haldarsaurav/Headway/docs/images/screen_boot.png

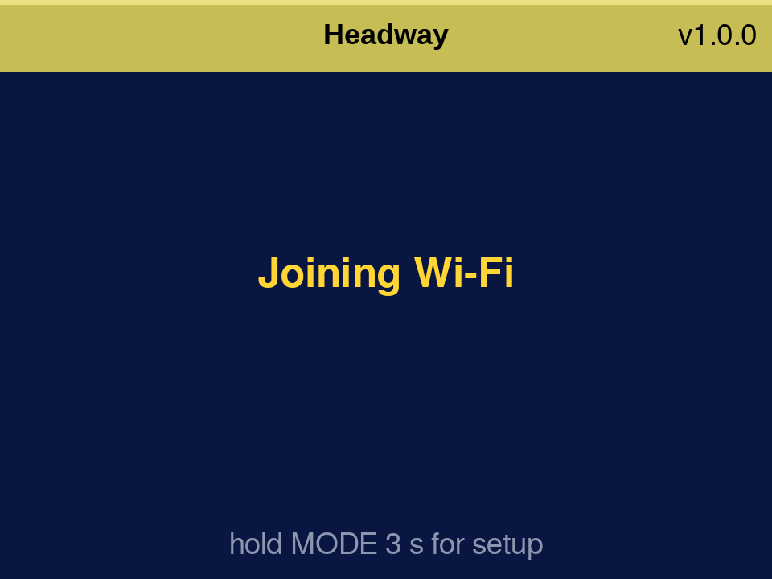
docs/images/screen_boot.png
