haldarsaurav/Headway/docs/previews_v1.2.6/A_2b_trains_p2.png

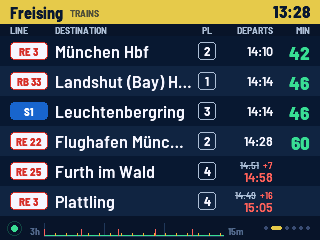
docs/previews_v1.2.6/A_2b_trains_p2.png
