haldarsaurav/Headway/docs/previews_v1.2.6/A_5_weather_stress.png

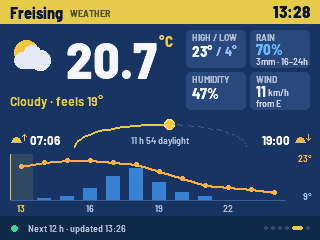
docs/previews_v1.2.6/A_5_weather_stress.png
