haldarsaurav/Headway/docs/previews_v1.2.6/A_6_outlook_stress.png

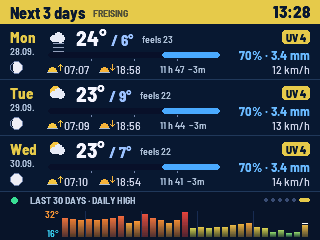
docs/previews_v1.2.6/A_6_outlook_stress.png
