haldarsaurav/Headway/docs/previews_v1.2.6/A_7_hold.png

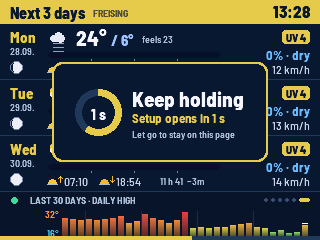
docs/previews_v1.2.6/A_7_hold.png
