haldarsaurav/Headway/docs/previews_v1.2.6/A_9_empty.png

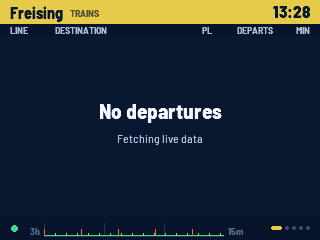
docs/previews_v1.2.6/A_9_empty.png
