haldarsaurav/Headway/docs/previews_v1.2.6/B_3_stadtbus_scroll.png

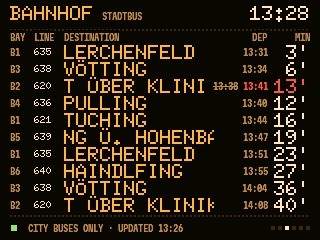
docs/previews_v1.2.6/B_3_stadtbus_scroll.png
