haldarsaurav/Headway/docs/previews_v1.2.6/B_4_pr_scroll.png

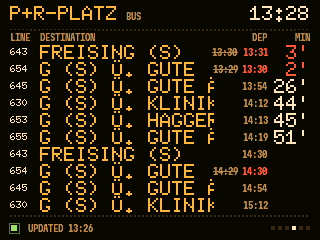
docs/previews_v1.2.6/B_4_pr_scroll.png
