haldarsaurav/Headway/docs/previews_v1.2.6/B_6_outlook_stress.png

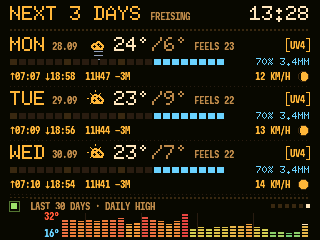
docs/previews_v1.2.6/B_6_outlook_stress.png
