haldarsaurav/Headway/docs/previews_v1.2.6/B_9_empty.png

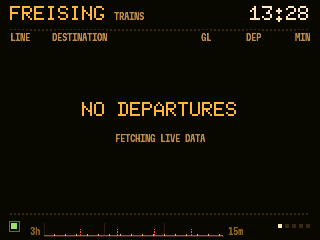
docs/previews_v1.2.6/B_9_empty.png
