haldarsaurav/Headway/docs/previews_v1.2.6/C_4_pr_scroll_stress.png

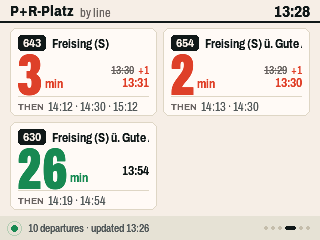
docs/previews_v1.2.6/C_4_pr_scroll_stress.png
