haldarsaurav/Headway/docs/previews_v1.2.6/C_7_hold.png

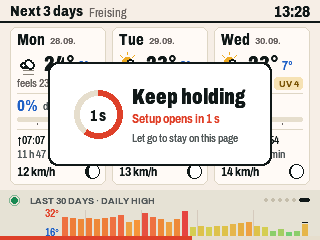
docs/previews_v1.2.6/C_7_hold.png
