haldarsaurav/Headway/docs/previews_v1.2.6/F_2_trains_flip.png

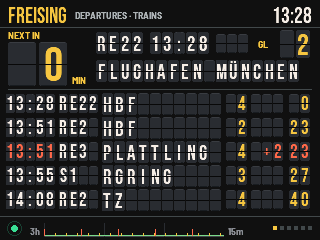
docs/previews_v1.2.6/F_2_trains_flip.png
