haldarsaurav/Headway/docs/previews_v1.2.6/F_3_stadtbus_flip.png

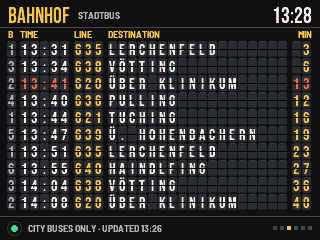
docs/previews_v1.2.6/F_3_stadtbus_flip.png
