haldarsaurav/Headway/docs/previews_v1.2.6/F_4_pr_flip.png

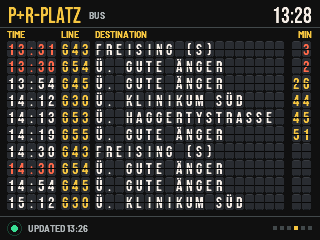
docs/previews_v1.2.6/F_4_pr_flip.png
