haldarsaurav/Headway/docs/previews_v1.2.6/F_6_outlook_flip_stress.png

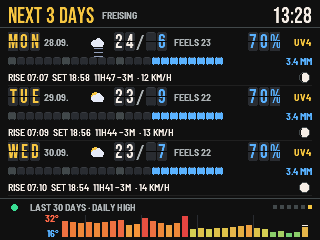
docs/previews_v1.2.6/F_6_outlook_flip_stress.png
