haldarsaurav/Headway/docs/previews_v1.2.6/F_7_hold.png

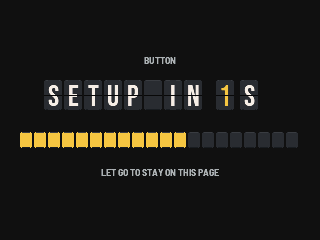
docs/previews_v1.2.6/F_7_hold.png
