haldarsaurav/Headway/docs/previews_v1.2.6/F_9_empty.png

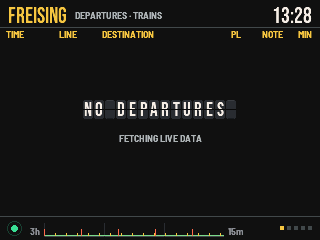
docs/previews_v1.2.6/F_9_empty.png
