haldarsaurav/Headway/docs/previews_v1.2.6/F_flipstress_last.png

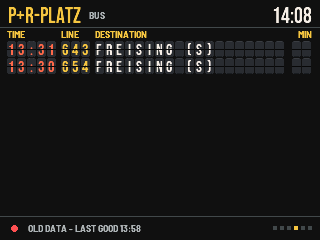
docs/previews_v1.2.6/F_flipstress_last.png
