haldarsaurav/Headway/docs/previews_v1.2.6/O_1_boot.png

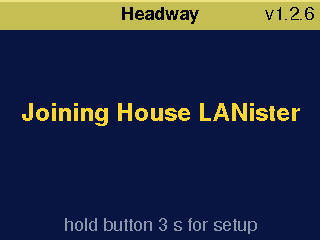
docs/previews_v1.2.6/O_1_boot.png
