haldarsaurav/Headway/docs/previews_v1.2.6/O_5_weather_stress.png

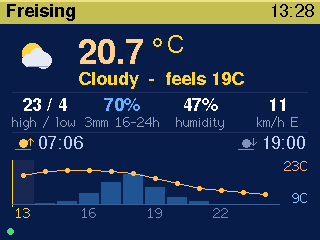
docs/previews_v1.2.6/O_5_weather_stress.png
