haldarsaurav/Headway/enclosure/slicer/modelA.png

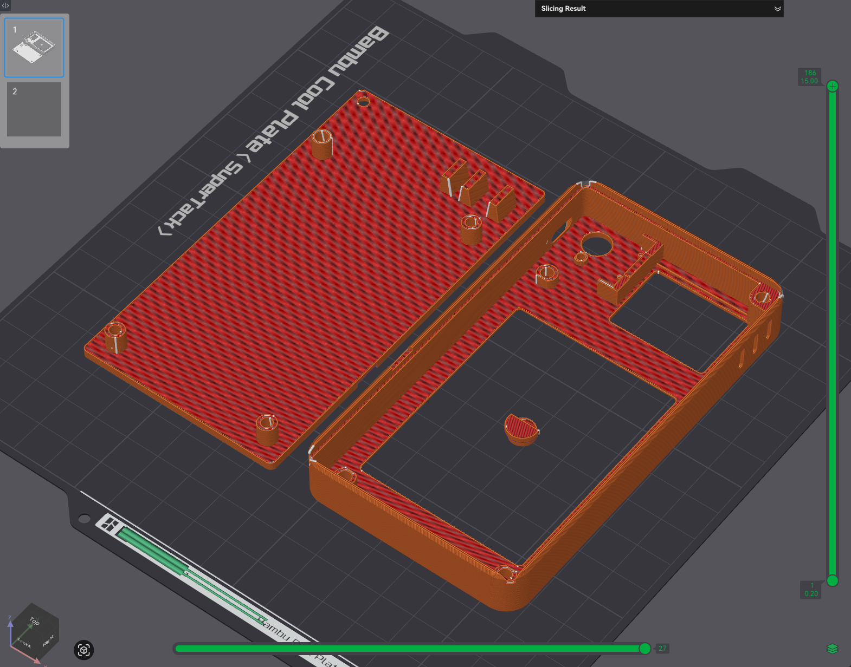
enclosure/slicer/modelA.png
