haldarsaurav/Headway/enclosure/slicer/modelB.png

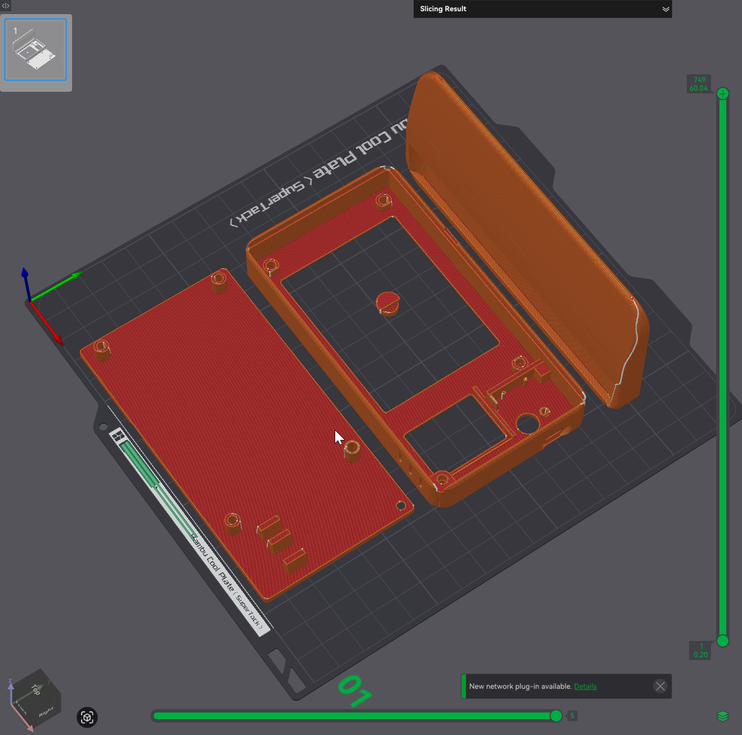
enclosure/slicer/modelB.png
