haldarsaurav/Headway/docs/previews_v1.2.6/A_8b_setup_phone.png

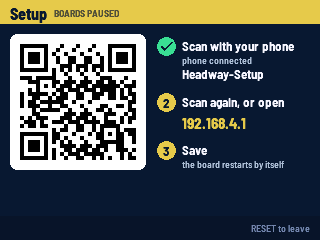
docs/previews_v1.2.6/A_8b_setup_phone.png
