haldarsaurav/Headway/docs/previews_v1.2.6/B_8b_setup_phone.png

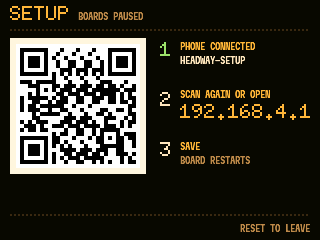
docs/previews_v1.2.6/B_8b_setup_phone.png
