haldarsaurav/Headway/docs/previews_v1.2.6/F_8b_setup_phone.png

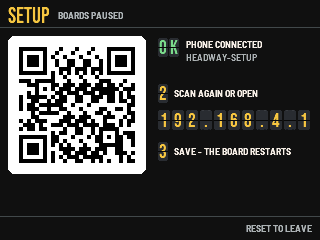
docs/previews_v1.2.6/F_8b_setup_phone.png
